dfashbaugh/Giant_Circuit_Playground/STLs/2ft_button.stl

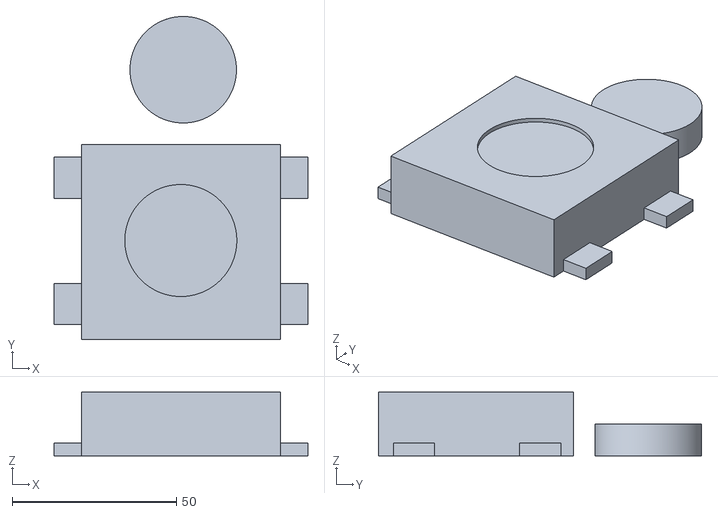
[picture p15: CAD file, 2016-10-16]
STLs/2ft_button.stl
77.3 x 98.3 x 19.4
