dfashbaugh/Giant_Circuit_Playground/STLs/4ft_slide_nub.stl

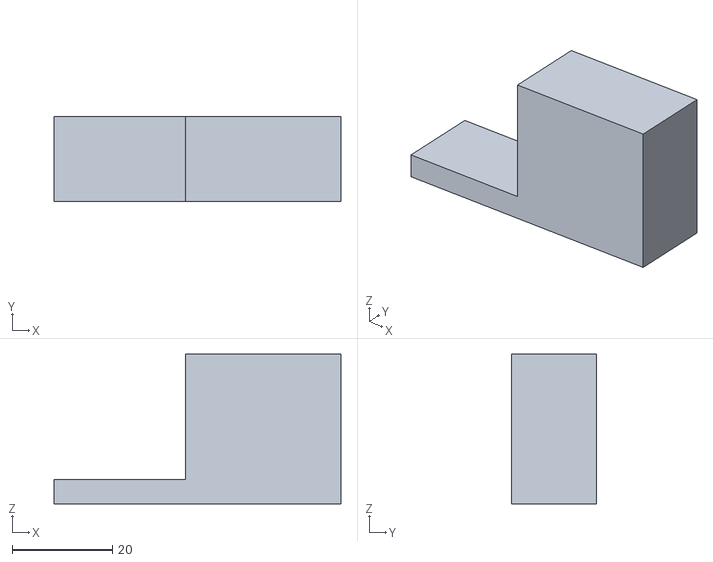
[picture p16: CAD file, 2016-10-16]
STLs/4ft_slide_nub.stl
57.4 x 17.0 x 30.0
